ovidiurosu90/psh-portable-smart-hangboard/Images/20240513_120411_cropped.png

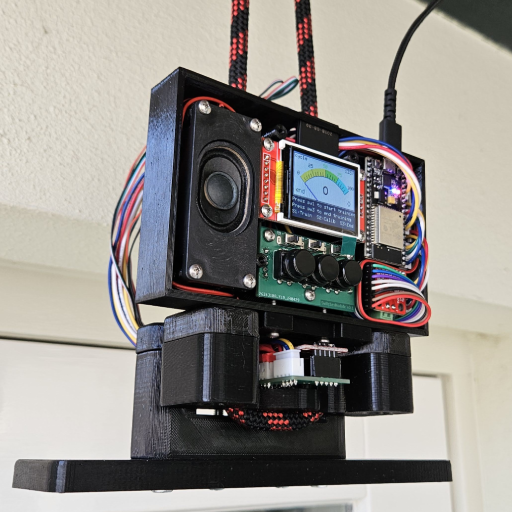
Images/20240513_120411_cropped.png
