ovidiurosu90/psh-portable-smart-hangboard/Images/PSH_Portable_Smart_Hangboard_May_2024_v3_2024-05-13_cropped.PNG

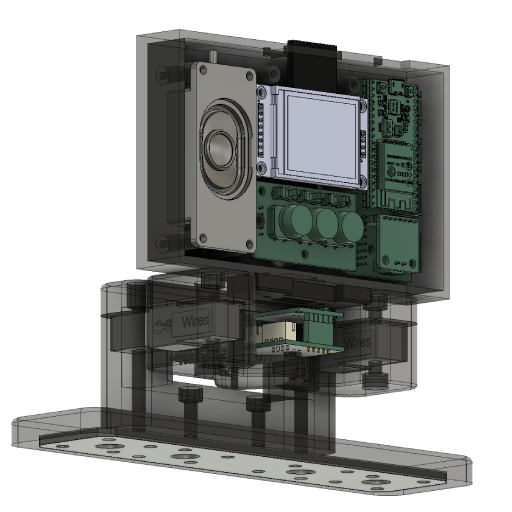
Images/PSH_Portable_Smart_Hangboard_May_2024_v3_2024-05-13_cropped.PNG
