ovidiurosu90/psh-portable-smart-hangboard/KiCad/MainControllerNodeMCU-32S/Screenshots/05_PCB Editor F.Cu fill zones.PNG

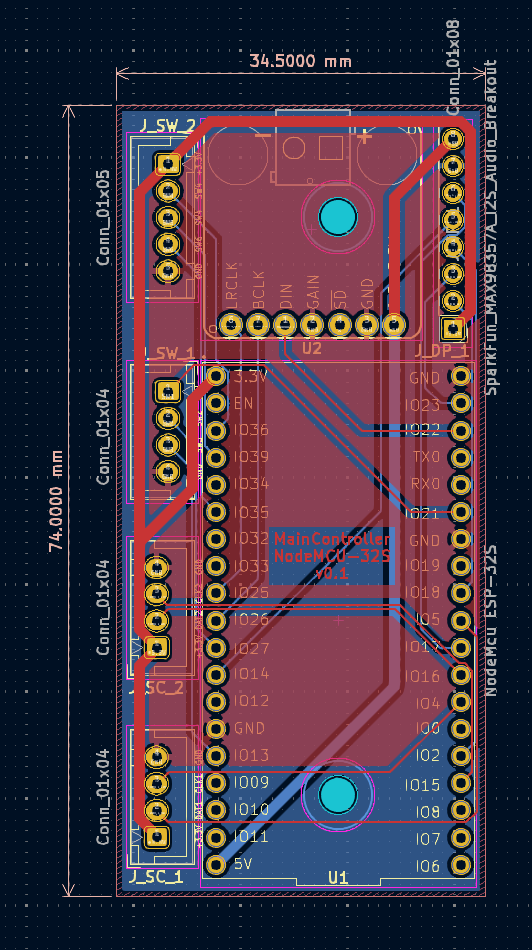
KiCad/MainControllerNodeMCU-32S/Screenshots/05_PCB Editor F.Cu fill zones.PNG
