ovidiurosu90/psh-portable-smart-hangboard/KiCad/MainControllerNodeMCU-32S/Screenshots/06_PCB Editor B.Cu fill zones.PNG

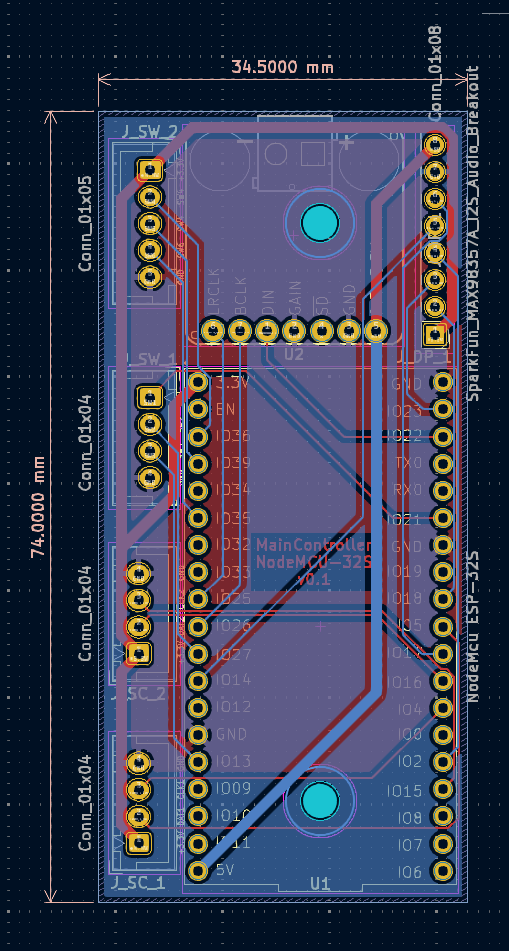
KiCad/MainControllerNodeMCU-32S/Screenshots/06_PCB Editor B.Cu fill zones.PNG
