ovidiurosu90/psh-portable-smart-hangboard/KiCad/MainControllerNodeMCU-32S/Screenshots/07_3D Viewer front.PNG

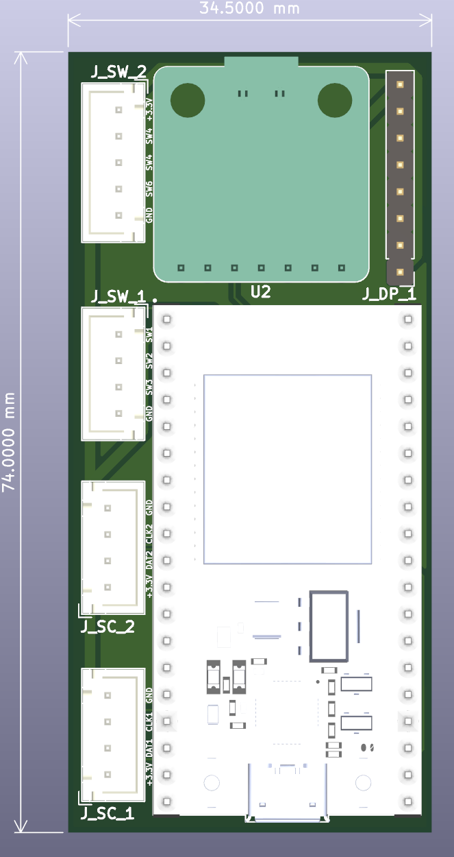
KiCad/MainControllerNodeMCU-32S/Screenshots/07_3D Viewer front.PNG
