ovidiurosu90/psh-portable-smart-hangboard/KiCad/MainControllerNodeMCU-32S/Screenshots/08_3D Viewer back.PNG

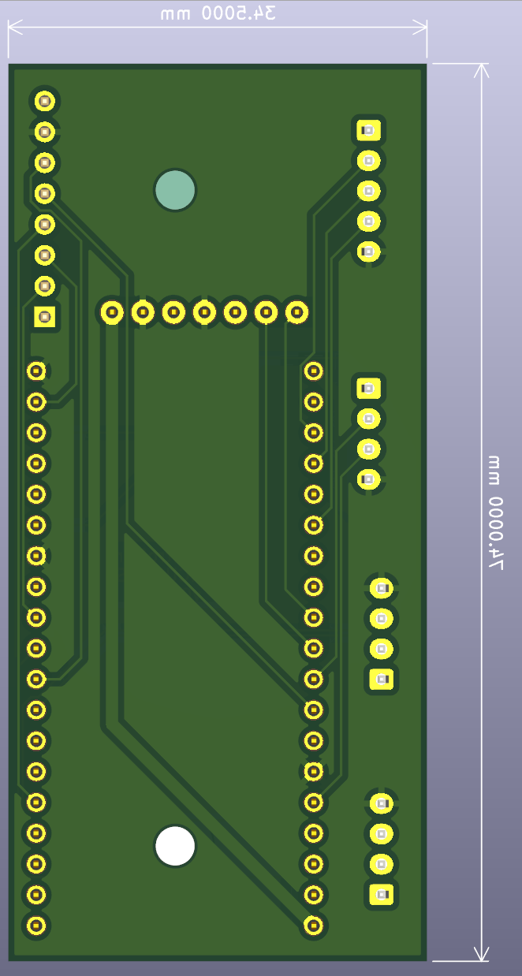
KiCad/MainControllerNodeMCU-32S/Screenshots/08_3D Viewer back.PNG
