ovidiurosu90/psh-portable-smart-hangboard/KiCad/MainControllerNodeMCU-32S/Screenshots/09_3D Viewer front no models.PNG

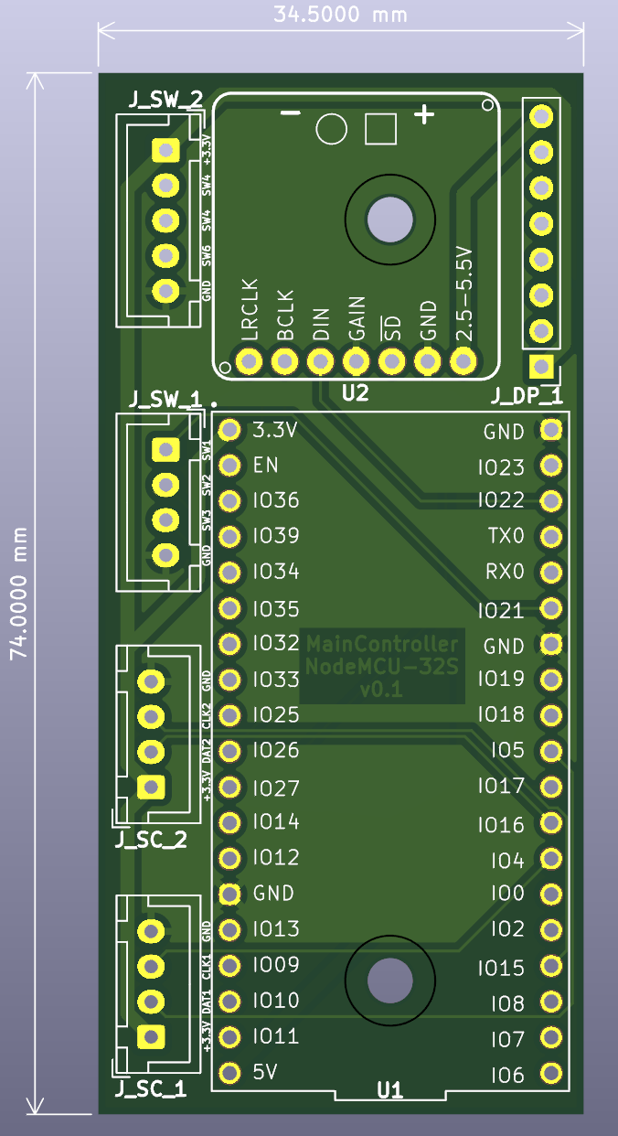
KiCad/MainControllerNodeMCU-32S/Screenshots/09_3D Viewer front no models.PNG
