ovidiurosu90/psh-portable-smart-hangboard/KiCad/ScaleModule/Screenshots/04_PCB Editor B.Cu unfill zones.PNG

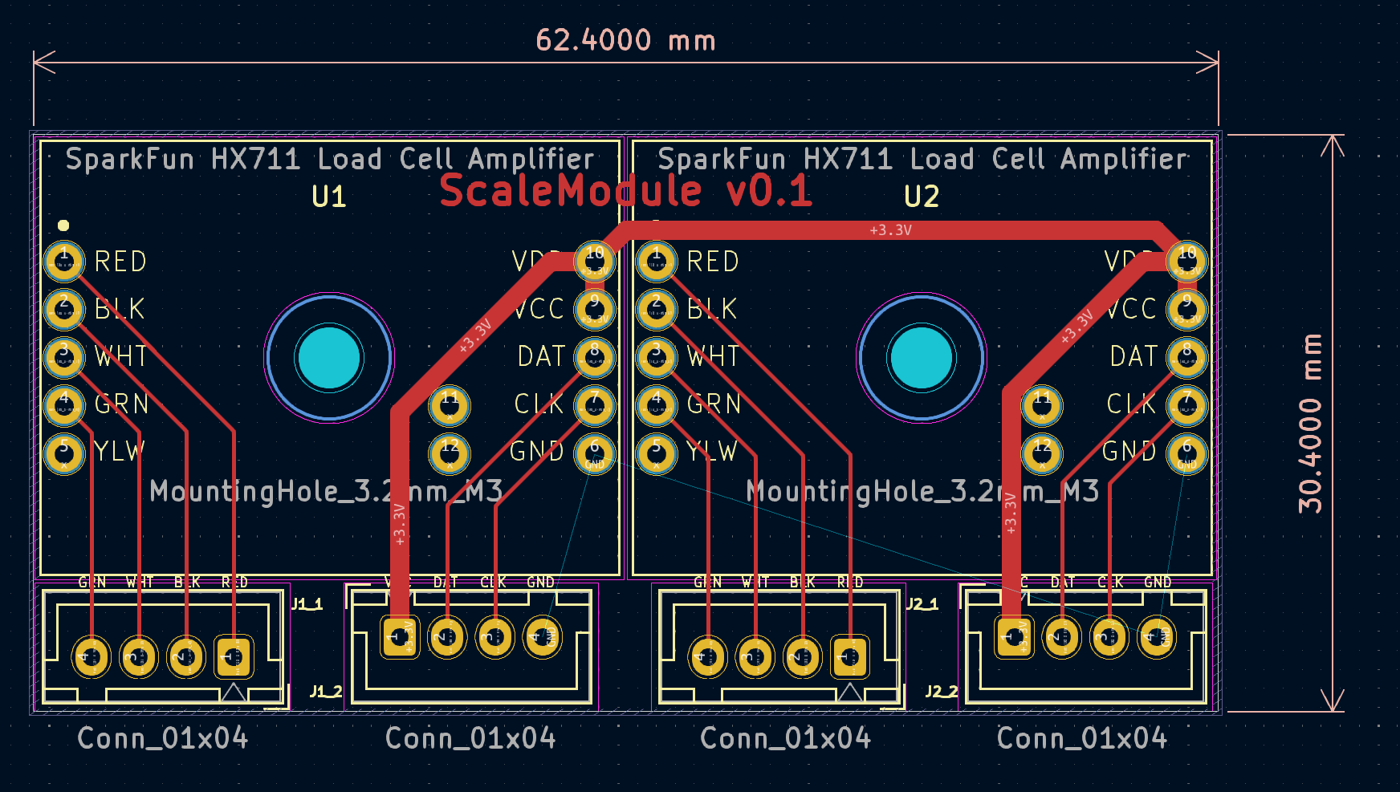
KiCad/ScaleModule/Screenshots/04_PCB Editor B.Cu unfill zones.PNG
