ovidiurosu90/psh-portable-smart-hangboard/KiCad/ScaleModule/Screenshots/05_PCB Editor F.Cu fill zones.PNG

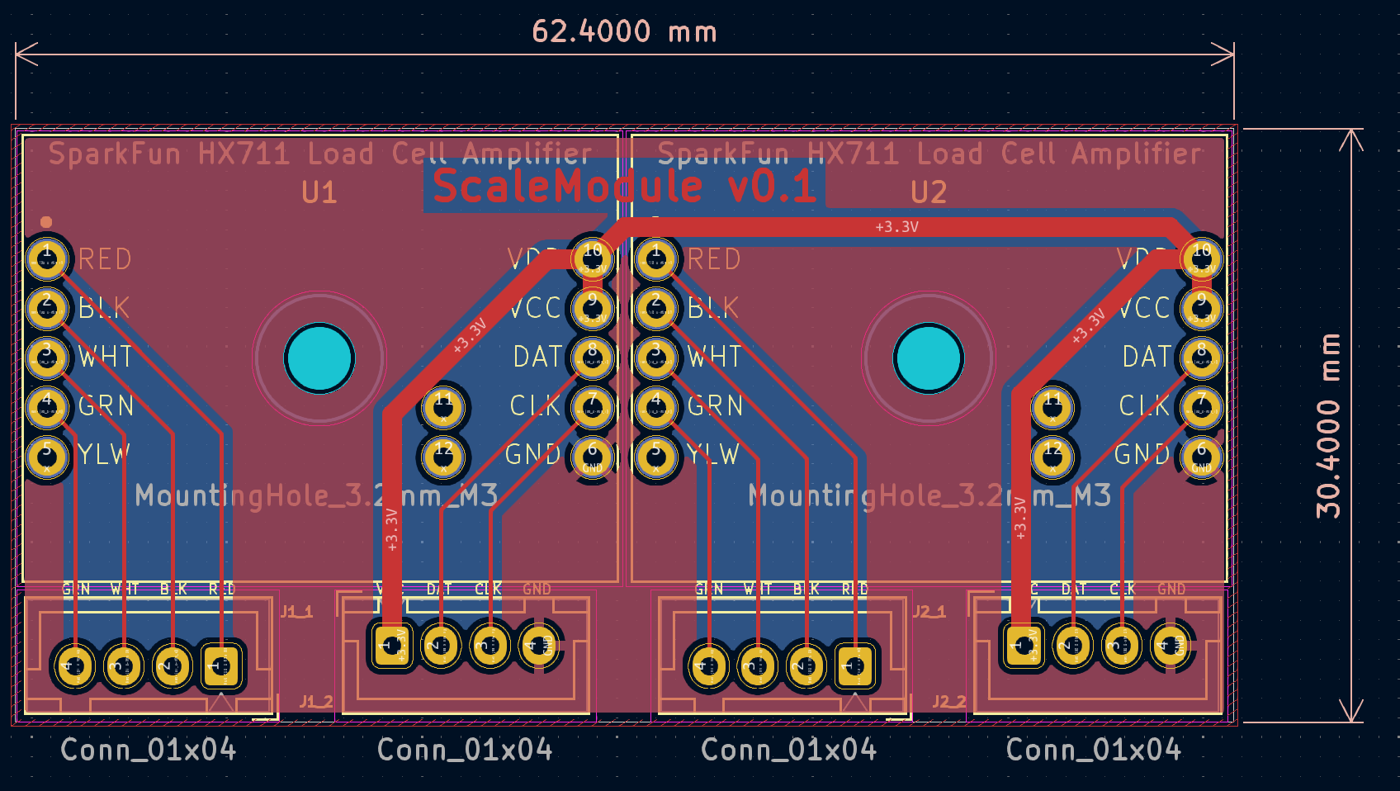
KiCad/ScaleModule/Screenshots/05_PCB Editor F.Cu fill zones.PNG
