ovidiurosu90/psh-portable-smart-hangboard/KiCad/ScaleModule/Screenshots/06_PCB Editor B.Cu fill zones.PNG

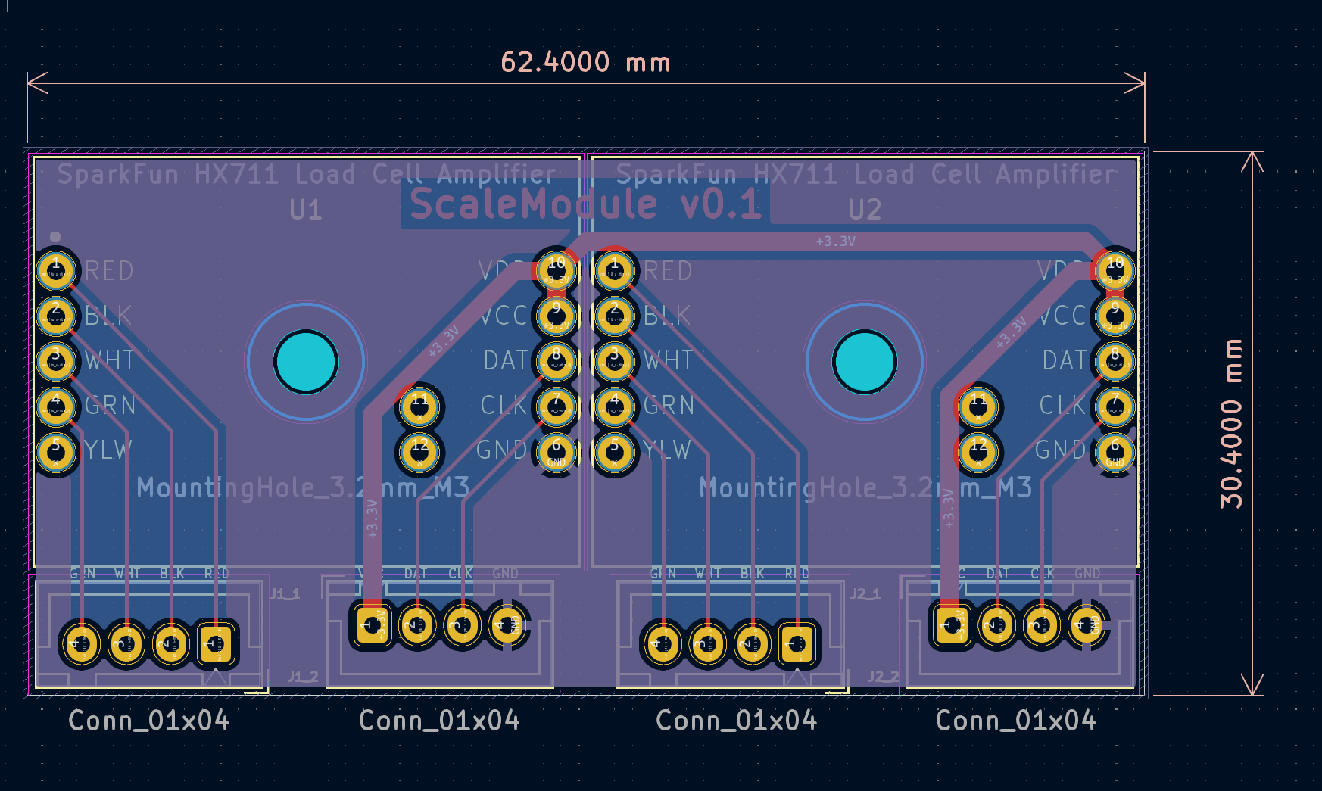
KiCad/ScaleModule/Screenshots/06_PCB Editor B.Cu fill zones.PNG
