ovidiurosu90/psh-portable-smart-hangboard/KiCad/ScaleModule/Screenshots/07_3D Viewer front.PNG

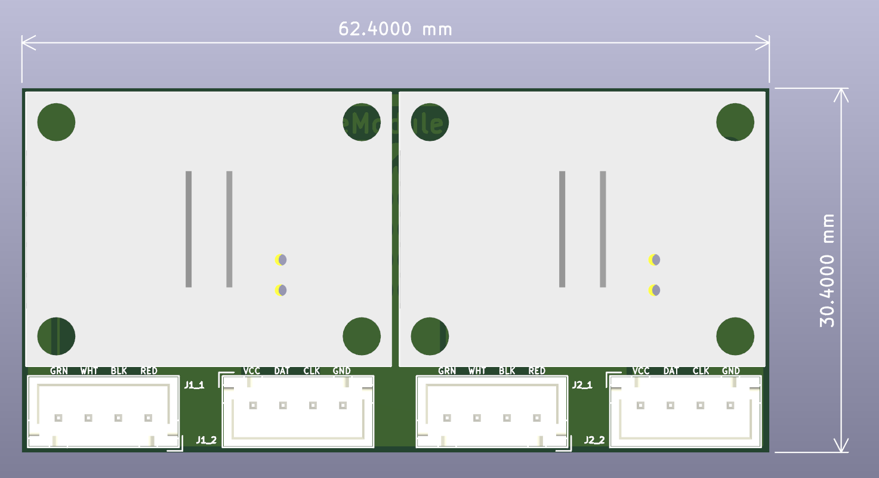
KiCad/ScaleModule/Screenshots/07_3D Viewer front.PNG
