ovidiurosu90/psh-portable-smart-hangboard/KiCad/ScaleModule/Screenshots/08_3D Viewer back.PNG

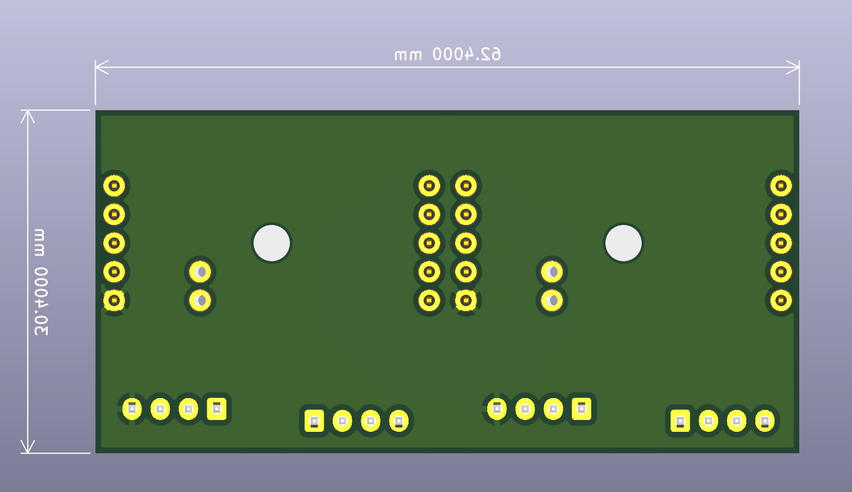
KiCad/ScaleModule/Screenshots/08_3D Viewer back.PNG
