ovidiurosu90/psh-portable-smart-hangboard/KiCad/ScaleModule/Screenshots/09_3D Viewer front no models.PNG

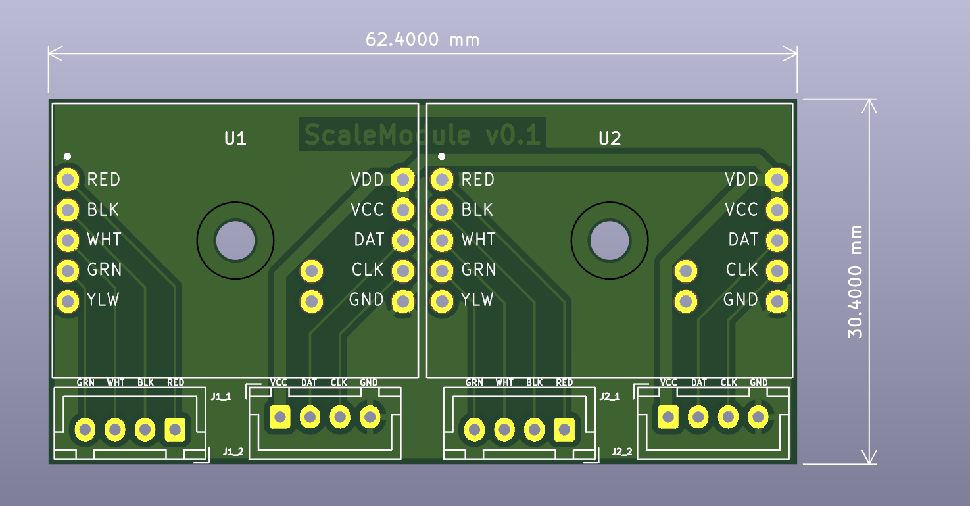
KiCad/ScaleModule/Screenshots/09_3D Viewer front no models.PNG
