ovidiurosu90/psh-portable-smart-hangboard/KiCad/ScaleModule/Screenshots/10_3D Viewer back no models.PNG

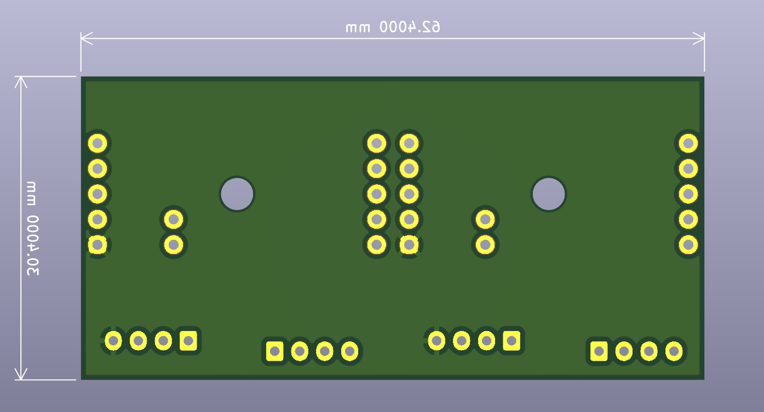
KiCad/ScaleModule/Screenshots/10_3D Viewer back no models.PNG
