ovidiurosu90/psh-portable-smart-hangboard/KiCad/SwitchesModule/Screenshots/02_Assign Footprints.PNG

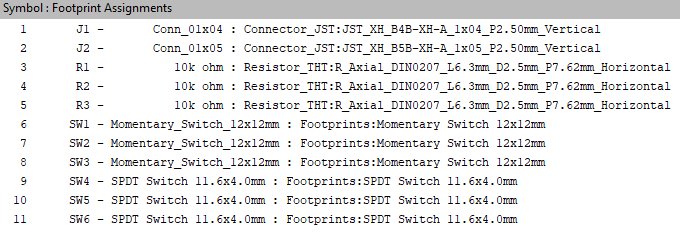
KiCad/SwitchesModule/Screenshots/02_Assign Footprints.PNG
