ovidiurosu90/psh-portable-smart-hangboard/KiCad/SwitchesModule/Screenshots/04_PCB Editor B.Cu unfill zones.PNG

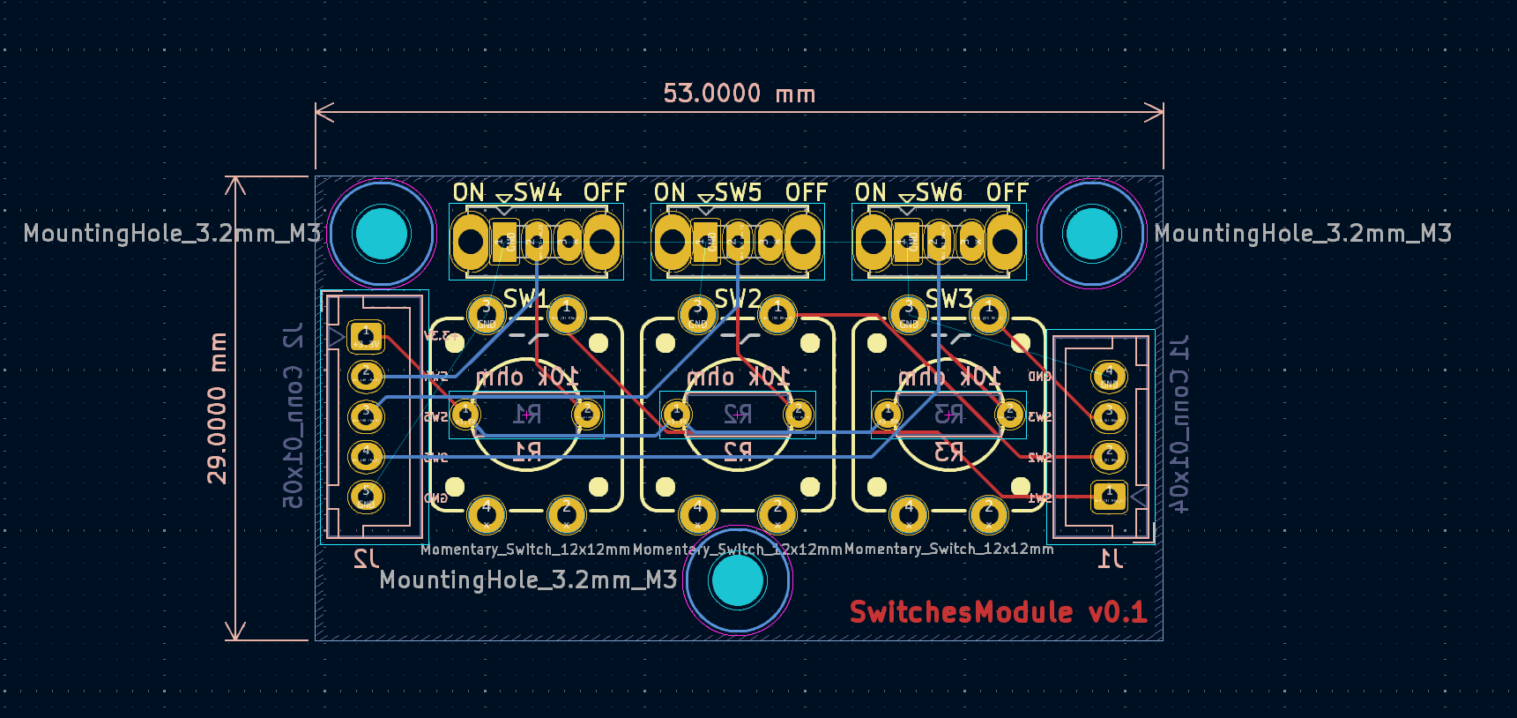
KiCad/SwitchesModule/Screenshots/04_PCB Editor B.Cu unfill zones.PNG
