ovidiurosu90/psh-portable-smart-hangboard/KiCad/SwitchesModule/Screenshots/05_PCB Editor F.Cu fill zones.PNG

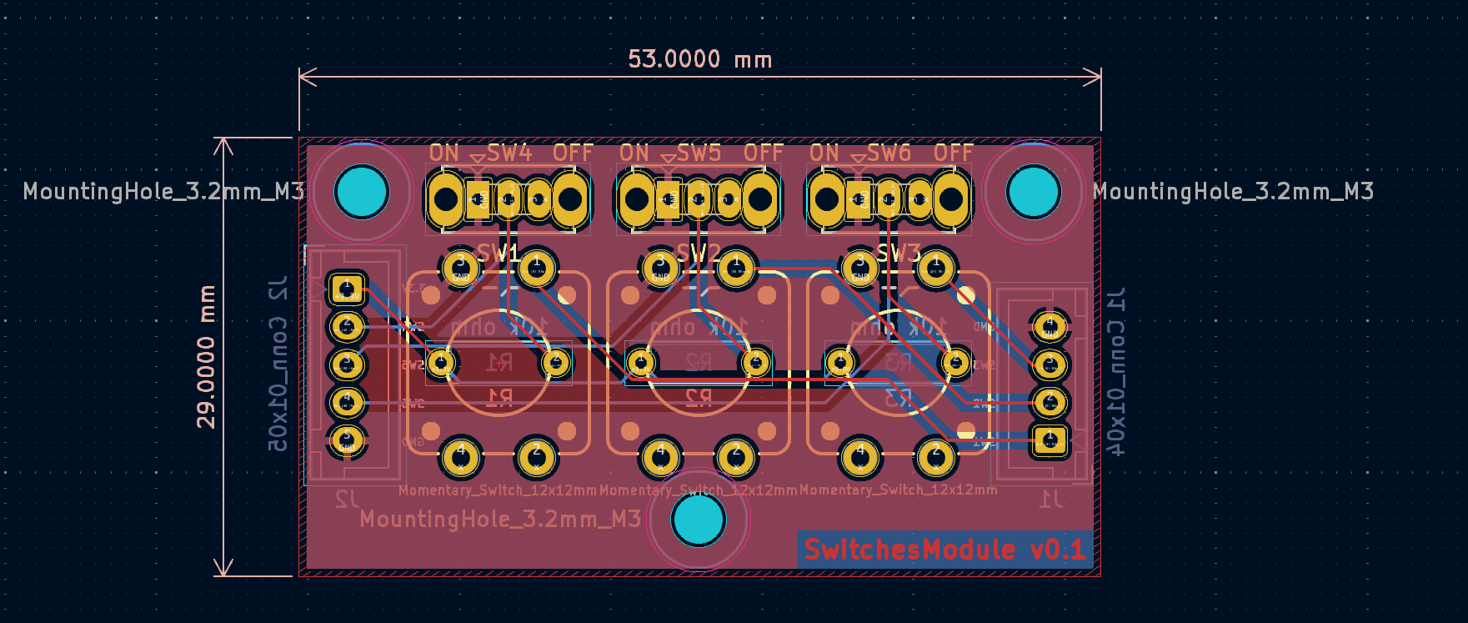
KiCad/SwitchesModule/Screenshots/05_PCB Editor F.Cu fill zones.PNG
