ovidiurosu90/psh-portable-smart-hangboard/KiCad/SwitchesModule/Screenshots/06_PCB Editor B.Cu fill zones.PNG

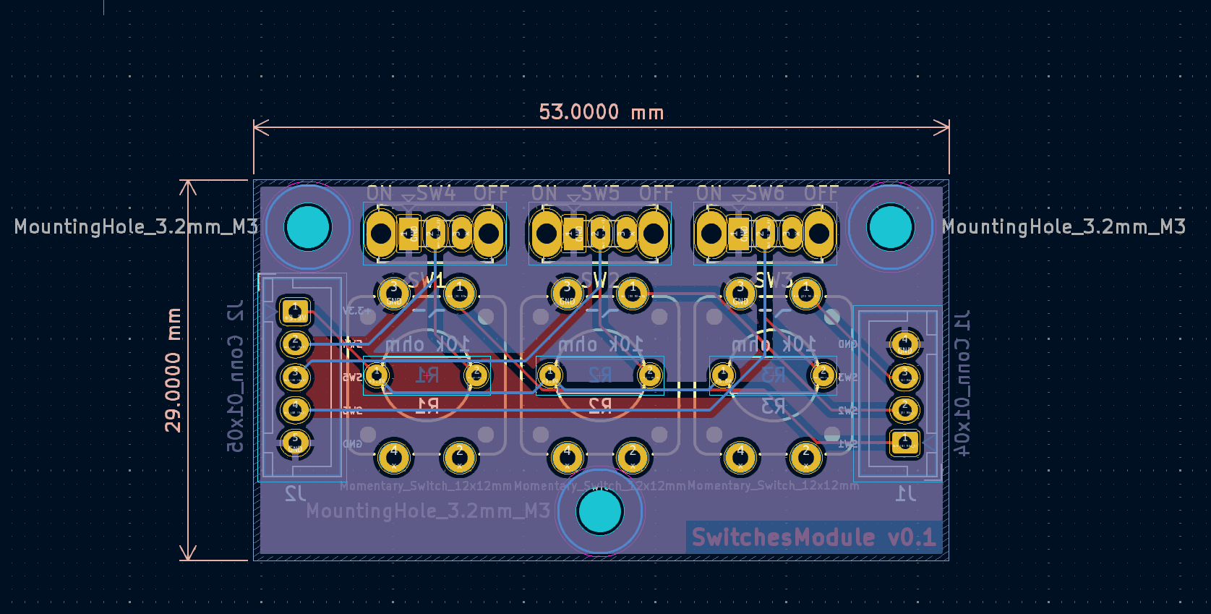
KiCad/SwitchesModule/Screenshots/06_PCB Editor B.Cu fill zones.PNG
