ovidiurosu90/psh-portable-smart-hangboard/KiCad/SwitchesModule/Screenshots/07_3D Viewer front.PNG

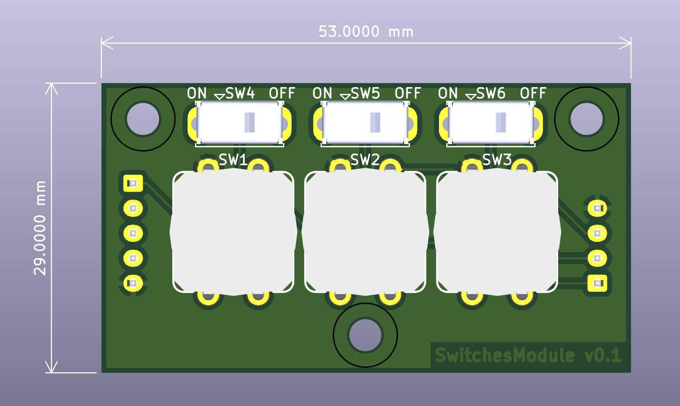
KiCad/SwitchesModule/Screenshots/07_3D Viewer front.PNG
