ovidiurosu90/psh-portable-smart-hangboard/KiCad/SwitchesModule/Screenshots/08_3D Viewer back.PNG

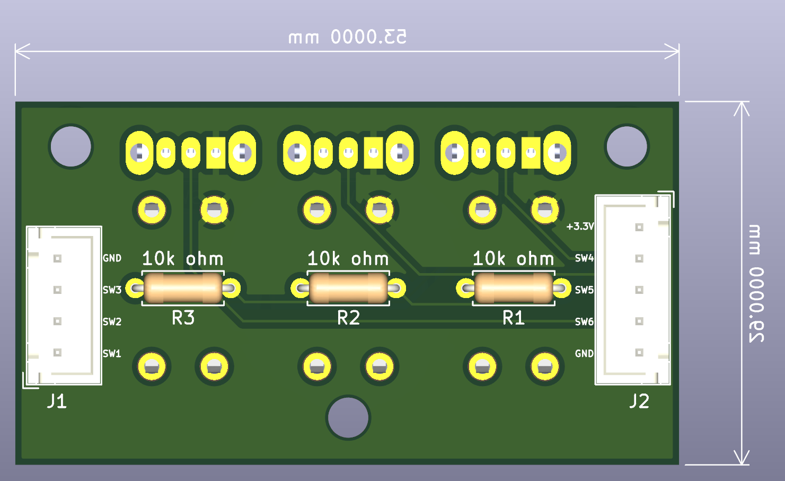
KiCad/SwitchesModule/Screenshots/08_3D Viewer back.PNG
