ovidiurosu90/psh-portable-smart-hangboard/KiCad/SwitchesModule/Screenshots/09_3D Viewer front no models.PNG

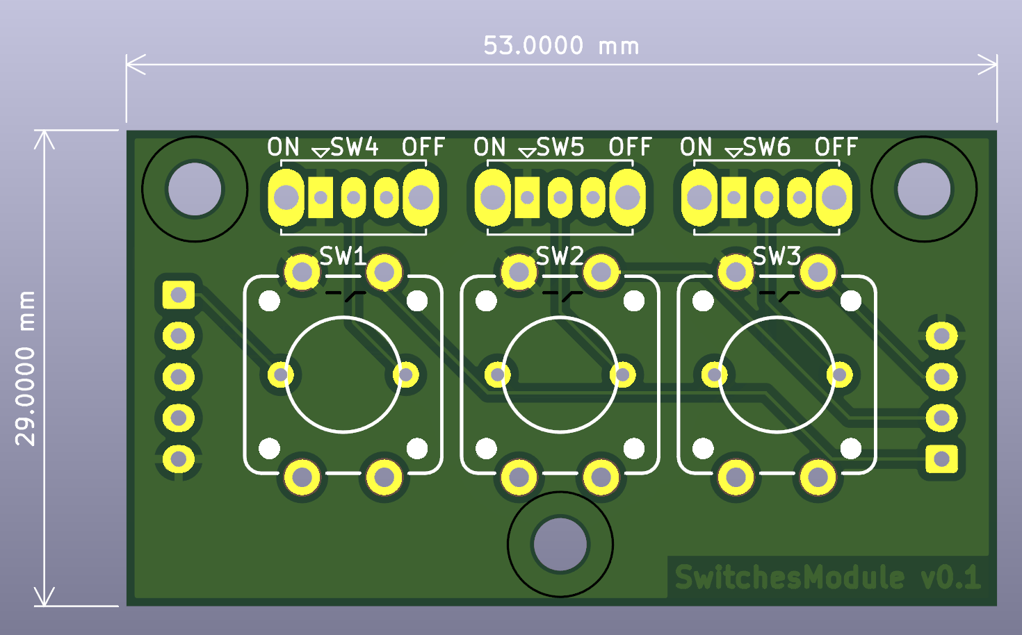
KiCad/SwitchesModule/Screenshots/09_3D Viewer front no models.PNG
