ovidiurosu90/psh-portable-smart-hangboard/KiCad/SwitchesModule/Screenshots/10_3D Viewer back no models.PNG

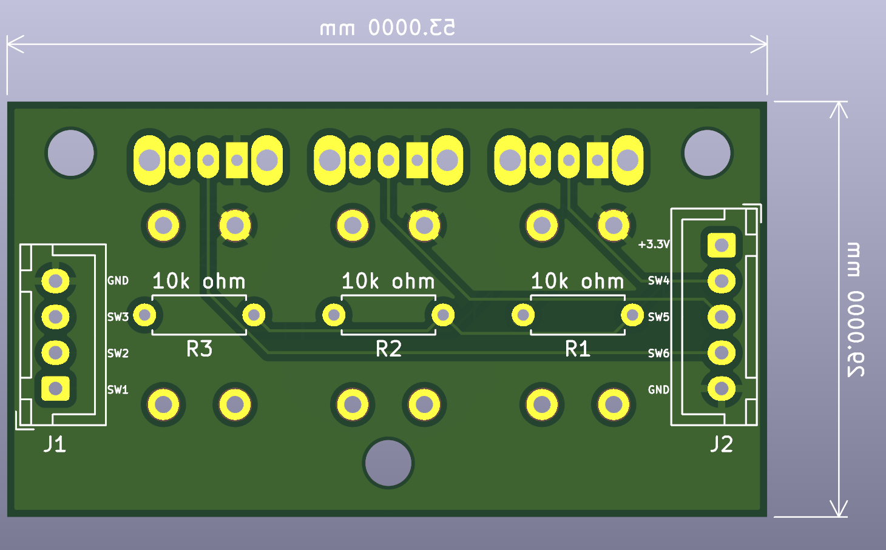
KiCad/SwitchesModule/Screenshots/10_3D Viewer back no models.PNG
