ovidiurosu90/psh-portable-smart-hangboard/Arduino/MainControllerNodeMCU-32S/before_upload.py

Import("env")
import serial, time

def before_upload(source, target, env):
    print("Sending '|' before upload...\n")
    ser = serial.Serial(env.subst("$UPLOAD_PORT"))
    msg = "|\n"
    ser.write(msg.encode())
    ser.flush()
    ser.close()
    time.sleep(1)

env.AddPreAction("upload", before_upload)
